psychogenic/LOGuvnor/hardware/LOGuvnor.kicad_sch

## KiCad design hardware/LOGuvnor.kicad_sch (2023-12-10)

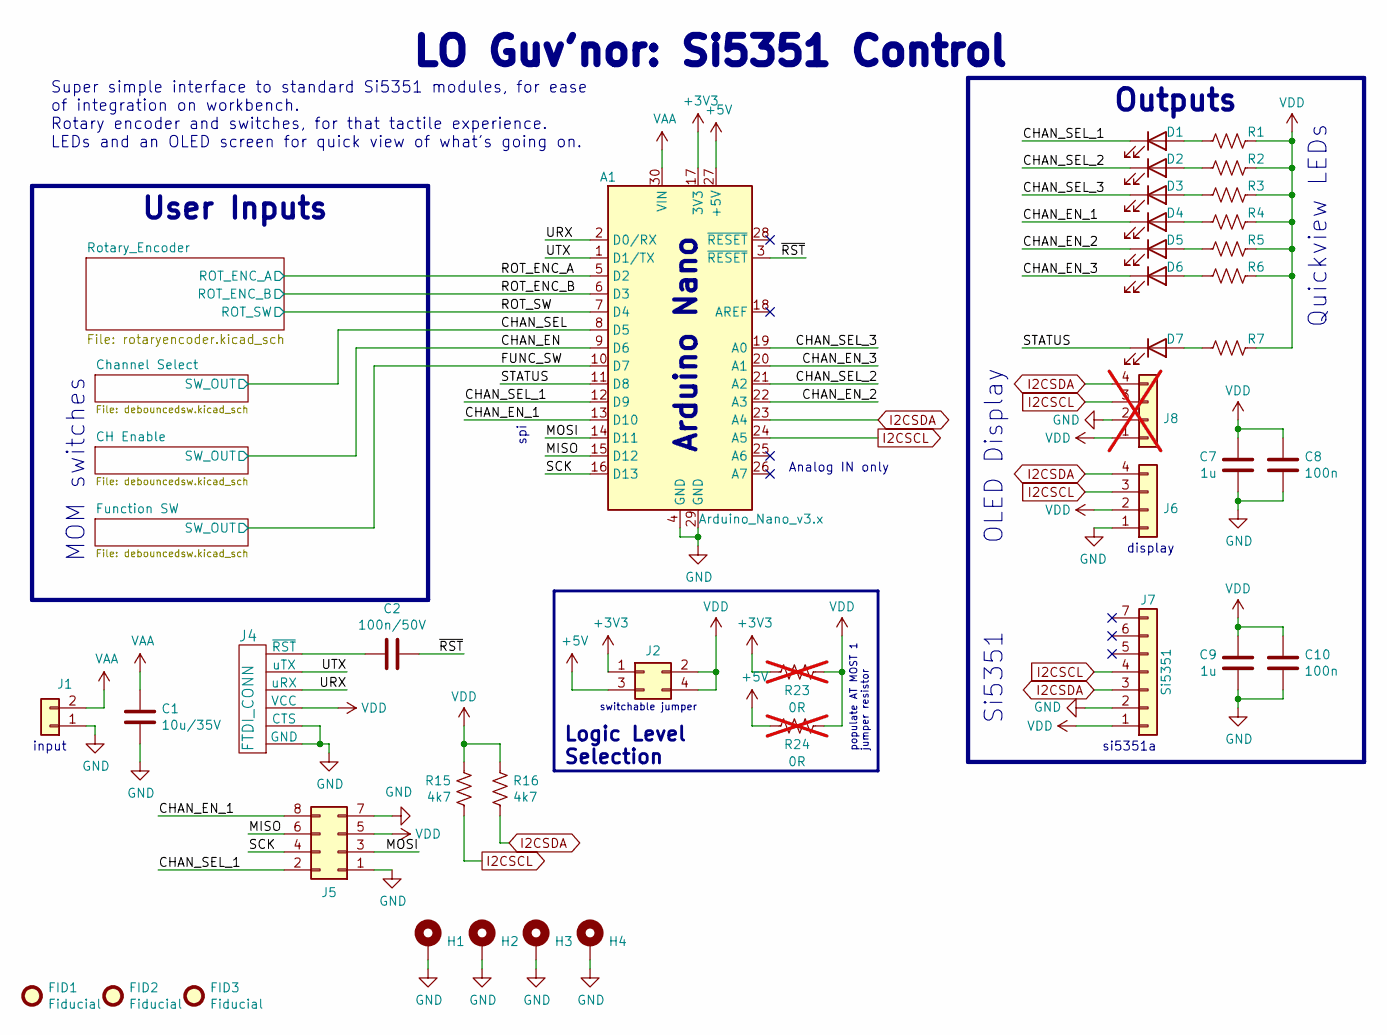
[picture p11: schematic LOGuvnor.kicad_sch]

Parts:
A1: Arduino_Nano_v3.x; Arduino_Nano
C1: C_10u_0603_35V; C_0603_1608Metric
C2, C8, C10: C_100n_0603_50V; C_0603_1608Metric
C7, C9: C_1u_0603_50V; C_0603_1608Metric
D1, D2, D3, D4, D5, D6, D7: LED; LED_0603_1608Metric
FID1, FID2, FID3: Fiducial; Fiducial_1mm_Mask2mm
H1, H2, H3, H4: MountingHole_Pad; MountingHole_3.2mm_M3_Pad_TopBottom
J1: Conn_01x02; PinSocket_1x02_P2.54mm_Vertical
J2: Conn_02x02_Odd_Even; PinHeader_2x02_P2.54mm_Vertical
J4: FTDI_CONN; PinHeader_1x06_P2.54mm_Vertical
J5: Conn_02x04_Odd_Even; PinHeader_2x04_P2.54mm_Vertical
J6: Conn_01x04; PinSocket_1x04_P2.54mm_Vertical
J7: Si5351; Si5351aModule
J8: Conn_01x04; PinSocket_1x04_P2.54mm_Vertical; not fitted
R1, R2, R3, R4, R5, R6, R7: R_1k_0603; R_0603_1608Metric
R15, R16: R_4k7_0603; R_0603_1608Metric
R23, R24: R_0R_0603_JUMPER; R_0603_1608Metric; not fitted

Connections:
+3V3: A1.17 (3V3), J2.1, R23.1
+5V: A1.27 (+5V), J2.3, R24.1
CHAN_EN: A1.9 (D6)
CHAN_EN_1: A1.13 (D10), D4.1 (K), J5.8
CHAN_EN_2: A1.22 (A3), D5.1 (K)
CHAN_EN_3: A1.20 (A1), D6.1 (K)
CHAN_SEL: A1.8 (D5)
CHAN_SEL_1: A1.12 (D9), D1.1 (K), J5.2
CHAN_SEL_2: A1.21 (A2), D2.1 (K)
CHAN_SEL_3: A1.19 (A0), D3.1 (K)
FUNC_SW: A1.10 (D7)
GND: A1.4 (GND), A1.29 (GND), C1.2, C7.2, C8.2, C9.2, C10.2, H1.1, H2.1, H3.1, H4.1, J1.1, J4.1 (GND), J4.2 (CTS), J5.1, J5.7, J6.1, J7.2, J8.2
I2CSCL: A1.24 (A5), J6.3, J7.4, J8.3, R15.2
I2CSDA: A1.23 (A4), J6.4, J7.3, J8.4, R16.2
MISO: A1.15 (D12), J5.6
MOSI: A1.14 (D11), J5.3
unnamed: C2.2, J4.6 (~RST)
unnamed: D1.2 (A), R1.2
unnamed: D2.2 (A), R2.2
unnamed: D3.2 (A), R3.2
unnamed: D4.2 (A), R4.2
unnamed: D5.2 (A), R5.2
unnamed: D6.2 (A), R6.2
unnamed: D7.2 (A), R7.2
ROT_ENC_A: A1.5 (D2)
ROT_ENC_B: A1.6 (D3)
ROT_SW: A1.7 (D4)
SCK: A1.16 (D13), J5.4
STATUS: A1.11 (D8), D7.1 (K)
URX: A1.2 (D0/RX), J4.4 (uRX)
UTX: A1.1 (D1/TX), J4.5 (uTX)
VAA: A1.30 (VIN), C1.1, J1.2
VDD: C7.1, C8.1, C9.1, C10.1, J2.2, J2.4, J4.3 (VCC), J5.5, J6.2, J7.1, J8.1, R1.1, R2.1, R3.1, R4.1, R5.1, R6.1, R7.1, R15.1, R16.1, R23.2, R24.2
~RST: A1.3 (~RESET), C2.1

Notes on the sheet:
Outputs
User Inputs
input
OLED Display
Quickview LEDs
display
LO Guv'nor: Si5351 Control
switchable jumper
Logic Level Selection
Super simple interface to standard Si5351 modules, for ease of integration on workbench. Rotary encoder and switches, for that tactile experience. LEDs and an OLED screen for quick view of what's going on.
populate AT MOST 1 jumper resistor
Si5351
si5351a
spi
Arduino Nano
Analog IN only
MOM switches
