psychogenic/LOGuvnor/hardware/debouncedsw.kicad_sch

## KiCad design hardware/debouncedsw.kicad_sch (2023-12-10, an earlier design)

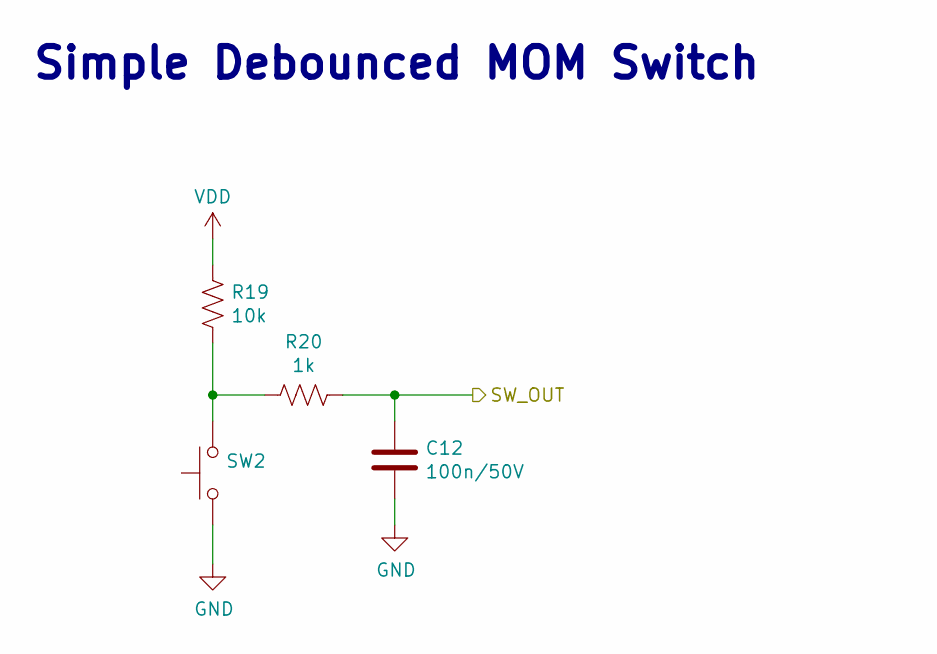
[picture p12: schematic debouncedsw.kicad_sch]

Parts:
C12: C_100n_0603_50V; C_0603_1608Metric
R19: R_10k_0603; R_0603_1608Metric
R20: R_1k_0603; R_0603_1608Metric
SW2: SW_Push_6x6; FSM2JSMA-6x6mm-SWITCH

Connections:
GND: C12.2, SW2.1
unnamed: R19.2, R20.2, SW2.2
SW_OUT: C12.1, R20.1
VDD: R19.1

Notes on the sheet:
Simple Debounced MOM Switch
