psychogenic/LOGuvnor/hardware/rotaryencoder.kicad_sch

## KiCad design hardware/rotaryencoder.kicad_sch (2023-12-10)

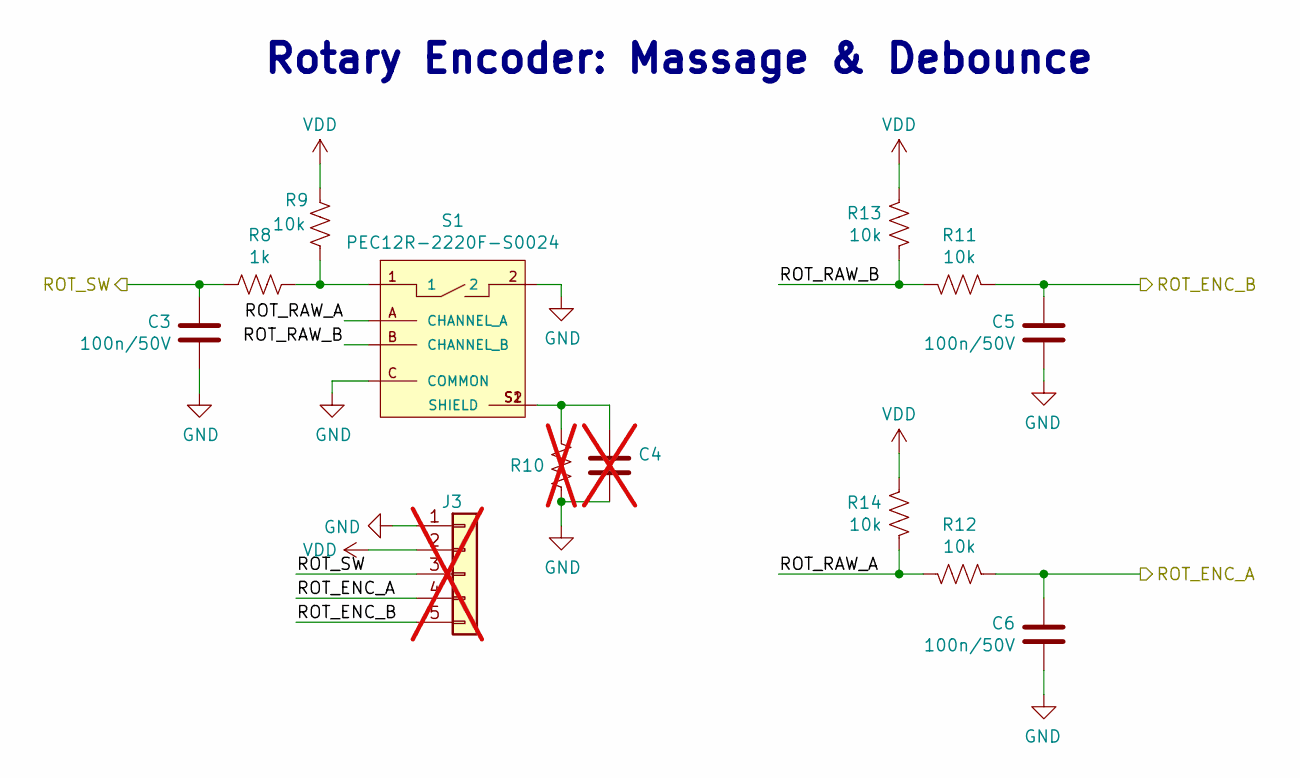
[picture p13: schematic rotaryencoder.kicad_sch]

Parts:
C3, C5, C6: C_100n_0603_50V; C_0603_1608Metric
C4: C_10n_0603_100V; C_0603_1608Metric; not fitted
J3: Conn_01x05; PinHeader_1x05_P2.54mm_Vertical; not fitted
R8: R_1k_0603; R_0603_1608Metric
R9, R11, R12, R13, R14: R_10k_0603; R_0603_1608Metric
R10: R_1M_0603; R_0603_1608Metric; not fitted
S1: PEC12R-2220F-S0024; XDCR_PEC12R-2220F-S0024

Connections:
GND: C3.2, C4.2, C5.2, C6.2, J3.1, R10.2, S1.2, S1.C (COMMON)
unnamed: C4.1, R10.1, S1.S1 (SHIELD), S1.S2 (SHIELD)
unnamed: R8.1, R9.2, S1.1
ROT_ENC_A: C6.1, J3.4, R12.2
ROT_ENC_B: C5.1, J3.5, R11.2
ROT_RAW_A: R12.1, R14.2, S1.A (CHANNEL_A)
ROT_RAW_B: R11.1, R13.2, S1.B (CHANNEL_B)
ROT_SW: C3.1, J3.3, R8.2
VDD: J3.2, R9.1, R13.1, R14.1

Notes on the sheet:
Rotary Encoder: Massage & Debounce
